har-in-air/ESP32C3_BLUETOOTH_AUDIO_VARIO/src/audio.h

#ifndef AUDIO_H_
#define AUDIO_H_

extern bool IsMuted;

void audio_set_frequency(int freqHz);
void audio_generate_tone(int freqHz, int ms);
void audio_beep(int freqHz, int onMs, int offMs, int numBeeps);
void audio_off();

#endif
