har-in-air/ESP32C3_BLUETOOTH_AUDIO_VARIO/src/ms5611.h

#ifndef MS5611_H_
#define MS5611_H_

//#define MS5611_TEST

// max conversion time with OSR=4096 is  9.04mS
#define MS5611_SAMPLE_PERIOD_MS         10

#define MS5611_READ_TEMPERATURE 		11
#define MS5611_READ_PRESSURE			22


#define MS5611_I2C_ADDRESS 0x77

#define MS5611_RESET      	0x1E
#define MS5611_CONVERT_D1 	0x40
#define MS5611_CONVERT_D2 	0x50
#define MS5611_ADC_READ   	0x00

#define MS5611_ADC_4096 	0x08

class MS5611 {        
public :
    MS5611();
    void trigger_pressure_sample(void);
    void trigger_temperature_sample(void);
    uint32_t  read_sample(void);
    void averaged_sample(int nSamples);
    void calculate_temperatureCx10(void);
    float calculate_pressurePa(void);
    void measure_noise(int nSamples);
    void reset(void);

    void get_calib_coefficients(void);
    float pa_to_cm(float pa);
    int  read_prom(void);
    uint8_t crc4(uint16_t* prom);
    int  sample_state_machine(void);
    void init_sample_state_machine(void);

    volatile float pressurePa;
    volatile float altitudeCm;
    float altitudeCmAvg;
    int  temperatureC;
    volatile int sensorState;

private :
    uint16_t prom[8];
    uint16_t cal[6];
    int64_t tref;
    int64_t offT1;
    int64_t sensT1;
    int32_t tempCx100;
    uint32_t D1;
    uint32_t D2;
    int64_t dT;
    };

#endif // MS5611_H_
