har-in-air/ESP32C3_BLUETOOTH_AUDIO_VARIO/src/pztbl.h

// Lookup table converting pressure in Pa to altitude in cm.
// Each LUT entry is the altitude in cm corresponding to an implicit
// pressure value, calculated as [PA_INIT - 1024*index] in Pa.
// The table is calculated for a nominal sea-level pressure  = 101325 Pa.
#include <Arduino.h>

#define PZLUT_ENTRIES   80
#define PA_INIT         106956
#define PA_DELTA        1024

const int32_t gPZTbl[PZLUT_ENTRIES] PROGMEM = {
-45853,
-37662,
-29407,
-21087,
-12700,
-4245,
4279,
12874,
21540,
30279,
39093,
47982,
56949,
65995,
75121,
84330,
93622,
102999,
112464,
122018,
131663,
141401,
151233,
161163,
171192,
181323,
191557,
201897,
212346,
222907,
233581,
244372,
255283,
266316,
277475,
288763,
300184,
311740,
323436,
335275,
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
};
