har-in-air/ESP32C3_BLUETOOTH_AUDIO_VARIO/src/ui.cpp

#include <Arduino.h>
#include <Ticker.h>
#include "config.h"
#include "audio.h"
#include "adc.h"
#include "nvd.h"
#include "ui.h"
#include "mpu9250.h"

Ticker     Tickr;

extern MPU9250 Imu;

volatile uint32_t BtnPCCAState;
volatile bool BtnPCCAPressed = false;
volatile bool BtnPCCALongPress = false;
	
void IRAM_ATTR btn_debounce() {
	BtnPCCAState = ((BtnPCCAState<<1) | ((uint32_t)BTN_PCCA()) );
	if ((BtnPCCAState | 0xFFFFFFF0) == 0xFFFFFFF8) {
		BtnPCCAPressed = true;
		}    
	if (BtnPCCAState == 0) {
		BtnPCCALongPress = true;
		}
	}

	
void ui_btn_init() {
 	Tickr.attach_ms(25, btn_debounce);
	ui_btn_clear();
	}
		

void ui_btn_clear() {
	BtnPCCAPressed  = false;
	BtnPCCALongPress = false;
	}

	
// !! Accelerometer calibration is REQUIRED for normal vario operation. !!
// If flash was completely erased, or Imu calibration data in flash was never initialized, or 
// imu calibration data is corrupt, the accel, mag and gyro biases are set to 0. Uncalibrated 
// state is indicated with a continuous sequence of alternating high and low beeps for 5 seconds.
void ui_indicate_uncalibrated_imu() {
	for (int cnt = 0; cnt < 5; cnt++) {
		audio_generate_tone(UNCALIBRATED_TONE_HZ, 500); 
		audio_generate_tone(UNCALIBRATED_TONE_HZ/2, 500);
		}
	}

	
// power-off indicated with a series of descending tones. 
void ui_indicate_power_off() {
	audio_generate_tone(1000,500);
	audio_generate_tone(500, 500);
	audio_generate_tone(250, 500);
	}

// error reading MS5611 calibration coefficients from PROM (CRC error) 
void ui_indicate_fault_MS5611() {
	for (int cnt = 0; cnt < 10; cnt++) {
		audio_generate_tone(MS5611_ERROR_TONE_HZ, 1000); 
		delay(100);
		}
	}

// error reading MPU9250 ID
void ui_indicate_fault_MPU9250() {
	for (int cnt = 0; cnt < 10; cnt++) {
		audio_generate_tone(MPU9250_ERROR_TONE_HZ, 1000); 
		delay(100);
		}
	}

void ui_indicate_battery_voltage(float batV) {
	int numBeeps;
	dbg_printf(("\r\nBattery voltage = %.2fV\r\n", batV ));

	if (batV >= 4.0f) numBeeps = 5;
	else
	if (batV >= 3.9f) numBeeps = 4;
	else
	if (batV >= 3.7f) numBeeps = 3;
	else
	if (batV >= 3.6f) numBeeps = 2;
	else numBeeps = 1;
	while (numBeeps--) {
		audio_generate_tone(BATTERY_TONE_HZ, 300);
		delay(300);
		}
	}
   

void ui_calibrate_accel(CALIB_PARAMS_t &calib) {    
    // acknowledge calibration button press with long tone
    audio_generate_tone(CALIBRATING_TONE_HZ, 3000);
    dbg_println(("-- Accelerometer calibration --"));
    dbg_println(("Place vario on a level surface with accelerometer z axis vertical and leave it undisturbed"));
    dbg_println(("You have 10 seconds, counted down with rapid beeps from 50 to 0"));
    for (int inx = 0; inx < 50; inx++) {
		delay(200); 
		dbg_println((50-inx));
		audio_generate_tone(CALIBRATING_TONE_HZ, 50);
		}
    dbg_println(("\r\nCalibrating accelerometer"));
    Imu.calibrate_accel(calib);
    dbg_println(("Accelerometer calibration done"));
    nvd_calib_store(calib);
    }


void ui_calibrate_gyro(CALIB_PARAMS_t &calib) {    
	dbg_println(("\r\nCalibrating gyro"));
	// normal power-on operation flow, always attempt to calibrate gyro. If calibration isn't possible because 
	// the unit is continuously disturbed (e.g. you turned on the unit while already flying), indicate this and
	// use the last saved gyro biases. Otherwise, save the new gyro biases to flash memory
	if (Imu.calibrate_gyro(calib)) {
		dbg_println(("Gyro calibration OK"));
		audio_generate_tone(CALIBRATING_TONE_HZ, 1000);
		nvd_calib_store(calib);
		}
	else { 
		dbg_println(("Gyro calibration failed"));
		audio_generate_tone(CALIBRATING_TONE_HZ, 1000);
		delay(500);
		audio_generate_tone(CALIBRATING_TONE_HZ/2, 1000);
		}
	}


	
#ifdef USE_9DOF_AHRS
void ui_calibrate_accel_gyro_mag() {  
	boolean bCalibrateAccel = false;
	boolean bCalibrateMag = false;
  	if ((Calib.axBias == 0) && (Calib.ayBias == 0) && (Calib.azBias == 0)) {
    	dbg_println(("! Uncalibrated accelerometer !"));
    	dbg_println(("Starting accelerometer calibration"));
		ui_calibrate_accel(Calib);
    	}
  	if ((Calib.mxBias == 0) && (Calib.myBias == 0) && (Calib.mzBias == 0)) {
    	dbg_println(("! Uncalibrated magnetometer !"));
    	dbg_println(("Starting magnetometer calibration"));
		ui_calibrate_mag(Calib);
    	}

	dbg_println(("Counting down to gyro calibration"));
	dbg_println(("Press the PCCA button to enforce accelerometer & magnetometer calibration first"));
	for (int inx = 0; inx < 5; inx++) {
		delay(500); 
		dbg_println((5-inx));
		if (digitalRead(pinPCCA) == 0) {
			bCalibrateAccel = true;
			bCalibrateMag = true;
			dbg_println(("PCCA button pressed"));
			break;
			}
		}
	if (bCalibrateAccel == true) {  
		ui_calibrate_accel(Calib);
		}
	if (bCalibrateMag == true) {  
		ui_calibrate_mag(Calib);
		}
	ui_calibrate_gyro(Calib);
	}
	

void ui_calibrate_mag(CALIB_PARAMS_t &calib) {    
    dbg_println(("-- Magnetometer calibration --"));
    dbg_println(("Rotate unit in all orientations in a figure of 8 fashion"));
    dbg_println(("Starting in 2 seconds."));
    for (int inx = 0; inx < 10; inx++) {
		delay(200); 
		dbg_println((5-inx));
		}
    dbg_println(("\r\nCalibrating magnetometer"));
    Imu.calibrate_mag(calib);
    dbg_println(("Magnetometer calibration done"));
    nvd_calib_store(calib);
    }
#else	

// Vario will attempt to calibrate gyro each time on power up. If the vario is disturbed, it will
// use the last saved gyro calibration values.
// The software delays a few seconds so that the unit can be left undisturbed for gyro calibration.
// This delay is indicated with a series of 10 short beeps. While it is beeping, if you press the
// PCCA button, the unit will calibrate the accelerometer and magnetometer first and then the gyro.
// As soon as you hear the long confirmation tone, release the button and
// put the unit in accelerometer calibration position resting undisturbed on a horizontal surface 
// with the accelerometer +z axis pointing vertically downwards. You will have some time 
// to do this, indicated by a series of beeps. After calibration, the unit will generate another 
// tone, save the calibration parameters to flash, and continue with normal vario operation
void ui_calibrate_accel_gyro() {  
	boolean bCalibrateAccel = false;
    // load the accel & gyro calibration parameters from the non-volatile data structure
  	if ((Calib.axBias == 0) && (Calib.ayBias == 0) && (Calib.azBias == 0)) {
    	dbg_println(("! Uncalibrated accelerometer !"));
    	ui_indicate_uncalibrated_imu(); 
		bCalibrateAccel = true;    
    	}
	if (bCalibrateAccel == true) {  
    	dbg_println(("Starting accelerometer calibration"));
		ui_calibrate_accel(Calib);
		bCalibrateAccel = false;
		}	
	dbg_println(("Counting down to gyro calibration"));
	dbg_println(("Press the PCCA button to enforce accelerometer calibration first"));
	for (int inx = 0; inx < 10; inx++) {
		delay(500); 
		dbg_println((10-inx));
		audio_generate_tone(CALIBRATING_TONE_HZ, 50); 
		if (digitalRead(pinPCCA) == 0) {
			bCalibrateAccel = true;
			dbg_println(("PCCA button pressed"));
			break;
			}
		}
	if (bCalibrateAccel == true) {  
		ui_calibrate_accel(Calib);
		}
	ui_calibrate_gyro(Calib);
	}
#endif
